Road-Balance/SpotMicroJetson/Images/jetsonNano.jpg

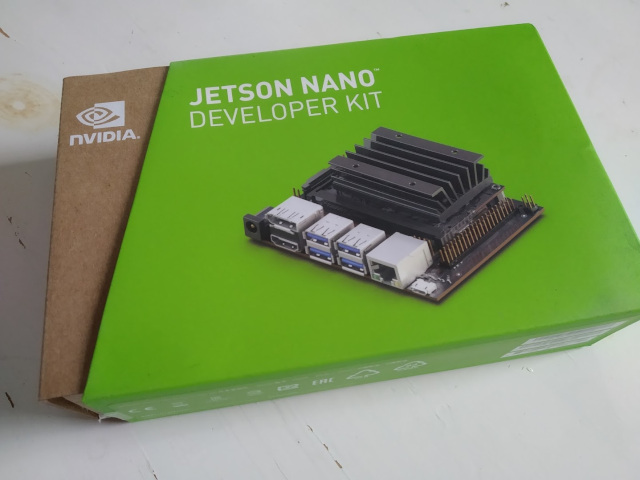
Images/jetsonNano.jpg
