Road-Balance/SpotMicroJetson/Images/jetsonNano_connected_1.jpg

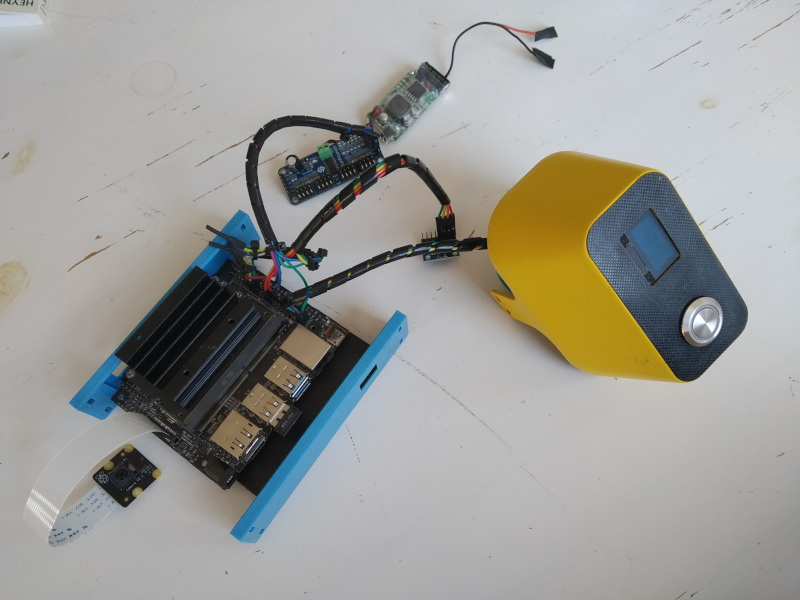
Images/jetsonNano_connected_1.jpg
