Road-Balance/SpotMicroJetson/Images/jetsonNanoCase.jpg

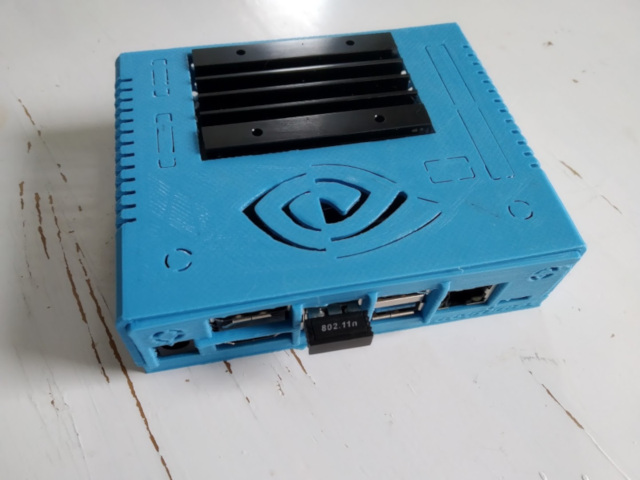
Images/jetsonNanoCase.jpg
