Road-Balance/SpotMicroJetson/Images/leg_front.jpg

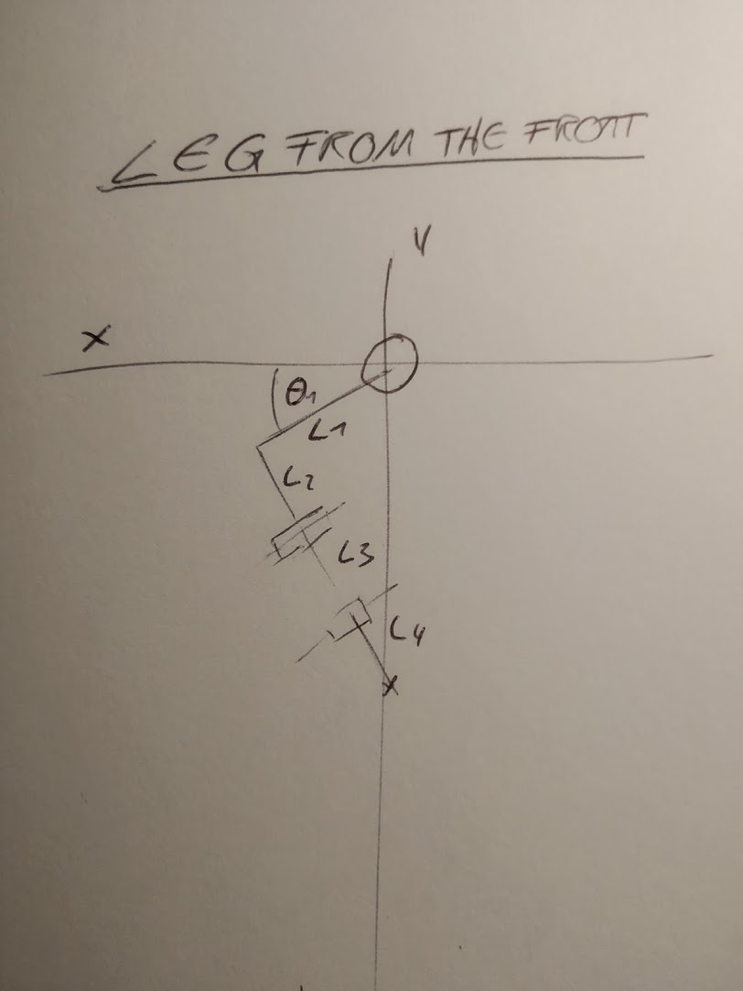
Images/leg_front.jpg
