Road-Balance/SpotMicroJetson/Images/leg_front_solved.jpg

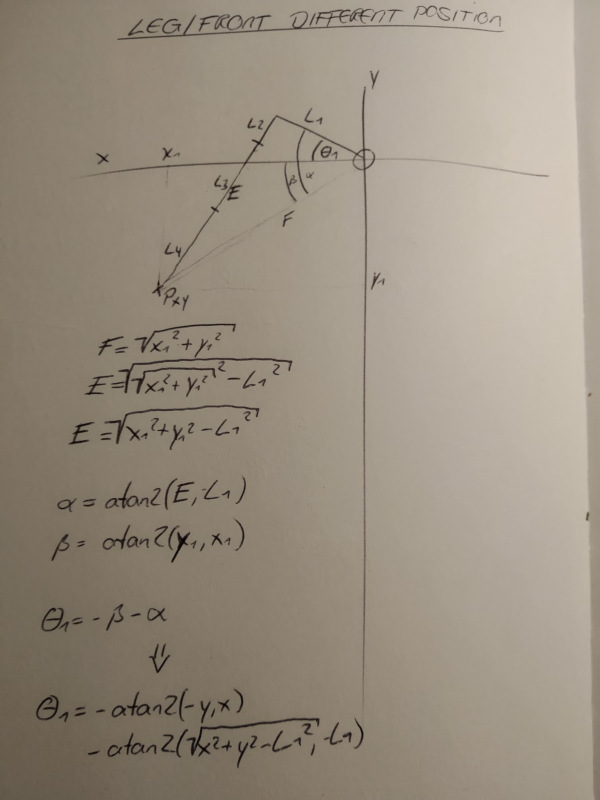
Images/leg_front_solved.jpg
