Road-Balance/SpotMicroJetson/Images/leg_in_space.jpg

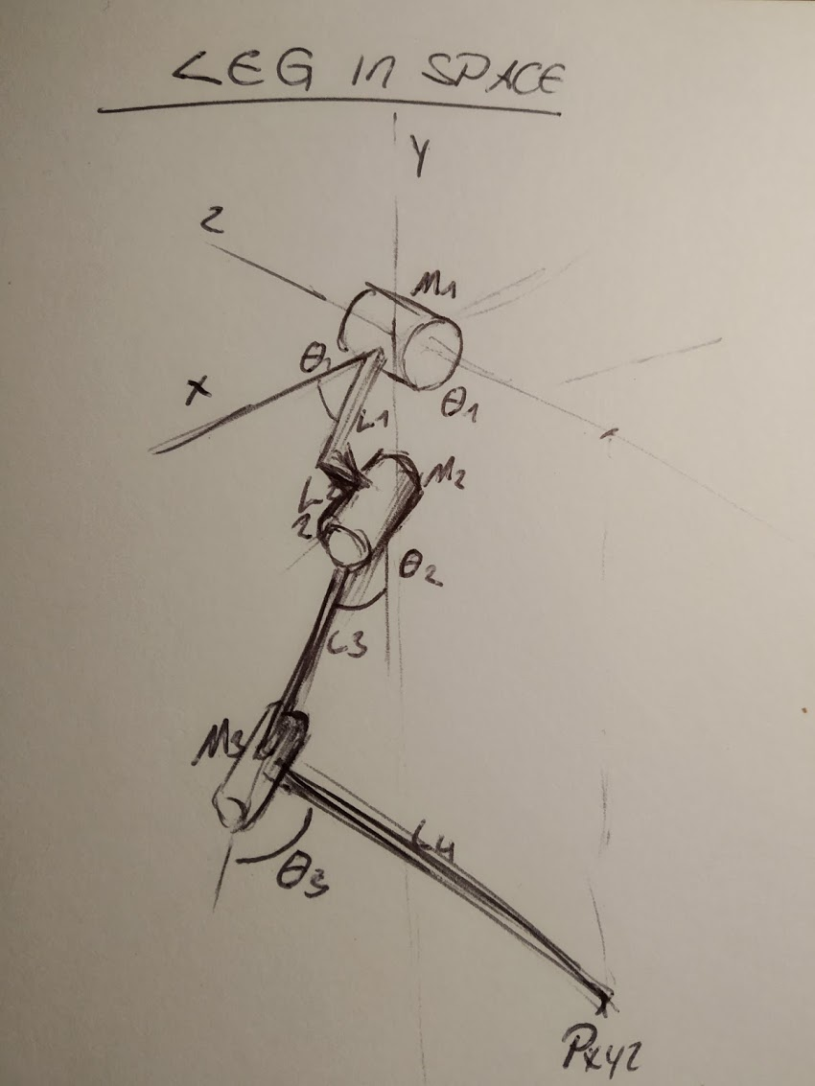
Images/leg_in_space.jpg
