Road-Balance/SpotMicroJetson/Images/leg_side.jpg

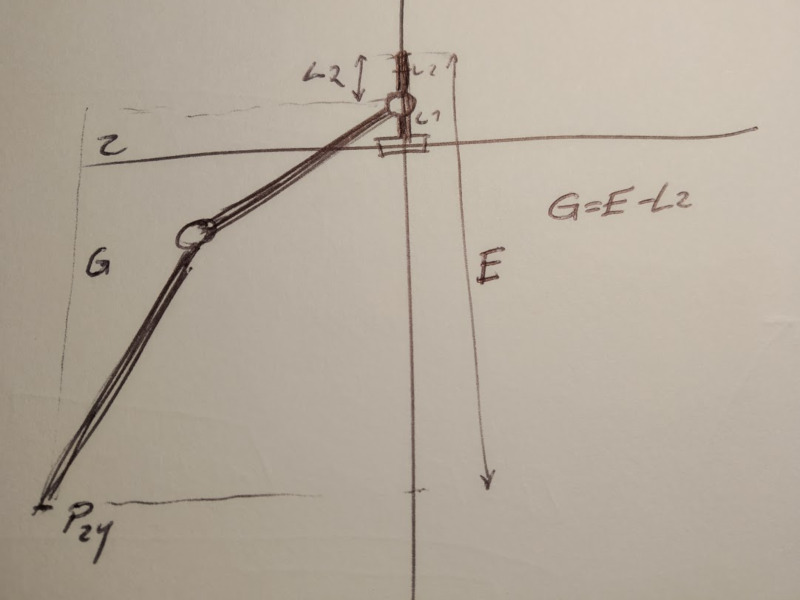
Images/leg_side.jpg
