Road-Balance/SpotMicroJetson/Images/leg_side_2.jpg

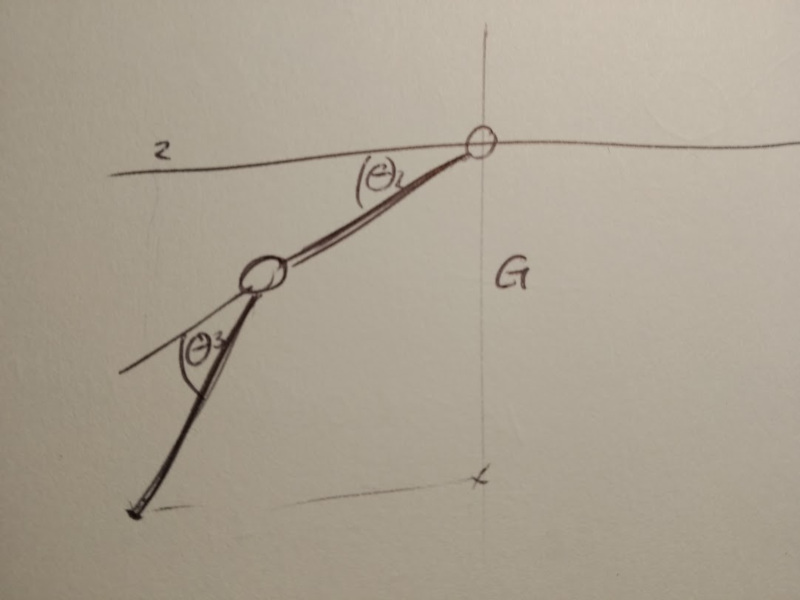
Images/leg_side_2.jpg
