Road-Balance/SpotMicroJetson/Images/leg_side_g.jpg

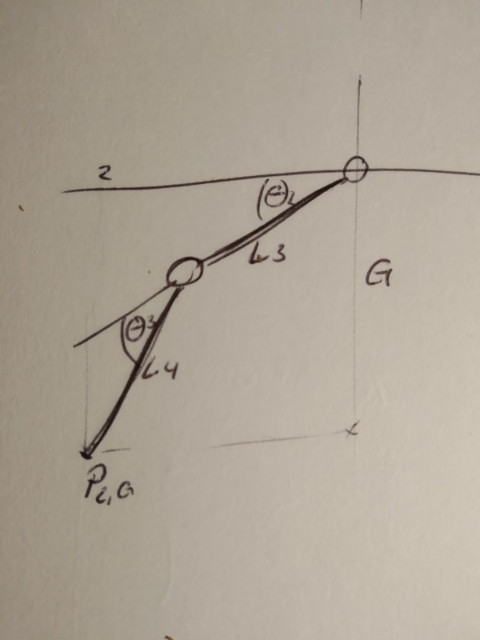
Images/leg_side_g.jpg
