Road-Balance/SpotMicroJetson/Images/SpotMicroAI_1.jpg

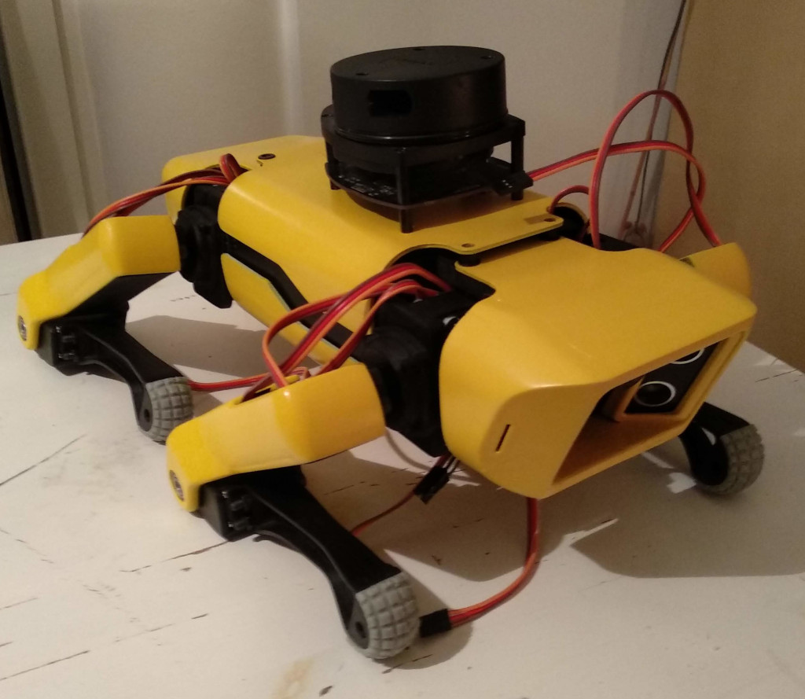
Images/SpotMicroAI_1.jpg
