Road-Balance/SpotMicroJetson/Images/SpotMicroAI_FreeCad.png

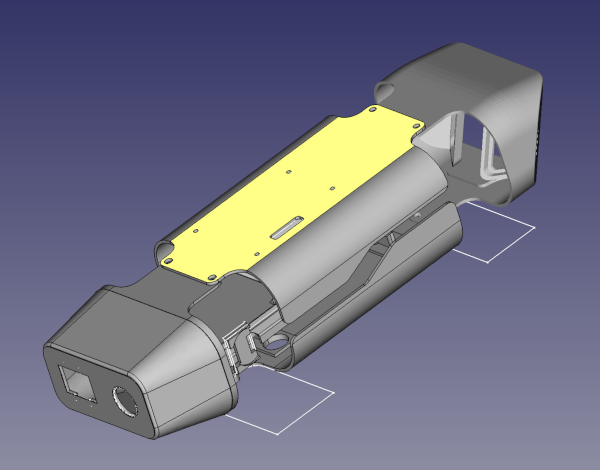
Images/SpotMicroAI_FreeCad.png
