Road-Balance/SpotMicroJetson/Images/SpotMicroAI_pybullet.png

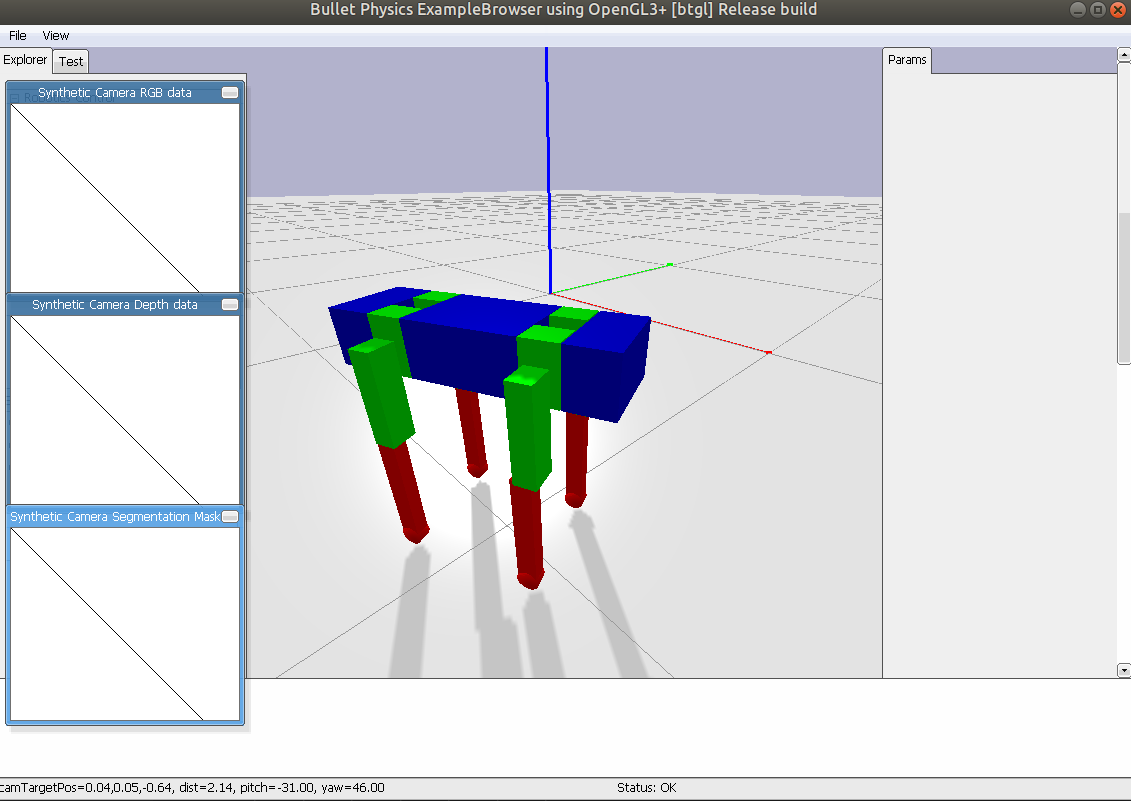
Images/SpotMicroAI_pybullet.png
