Road-Balance/SpotMicroJetson/Images/SpotMicroAI_pybullet_2.png

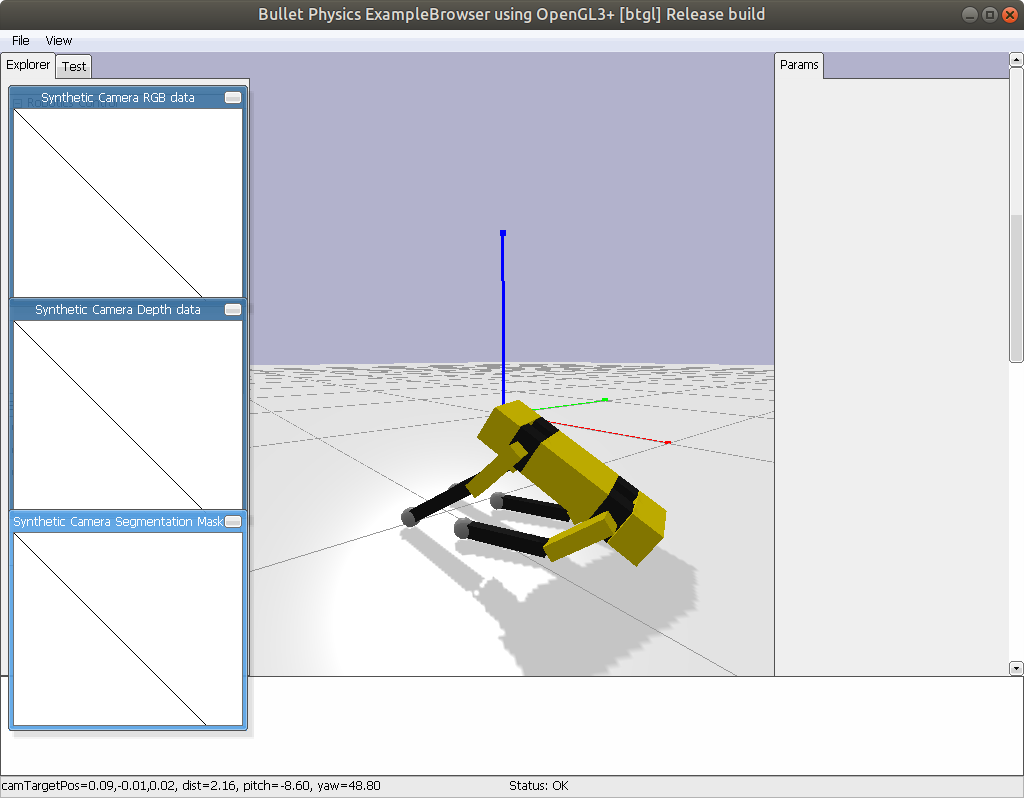
Images/SpotMicroAI_pybullet_2.png
