Road-Balance/SpotMicroJetson/Images/SpotMicroAI_pybullet_lidar2.png

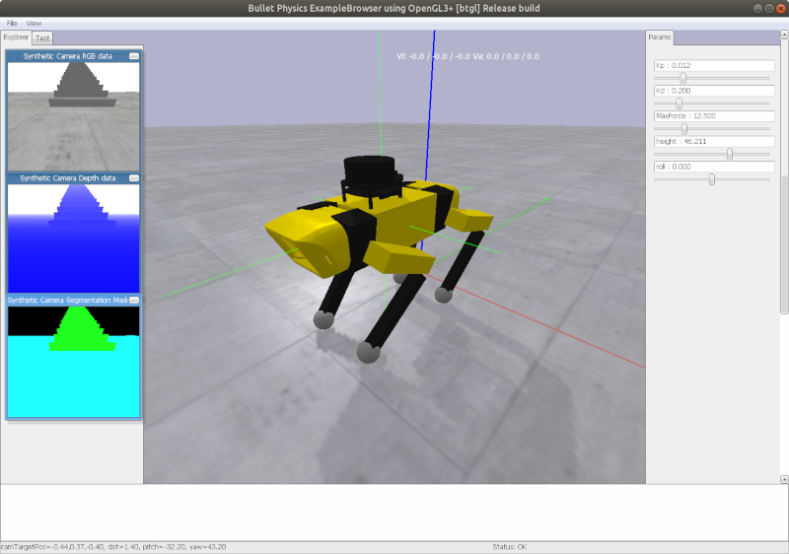
Images/SpotMicroAI_pybullet_lidar2.png
