Road-Balance/SpotMicroJetson/Images/SpotMicroAI_pybullet_lidar3.png

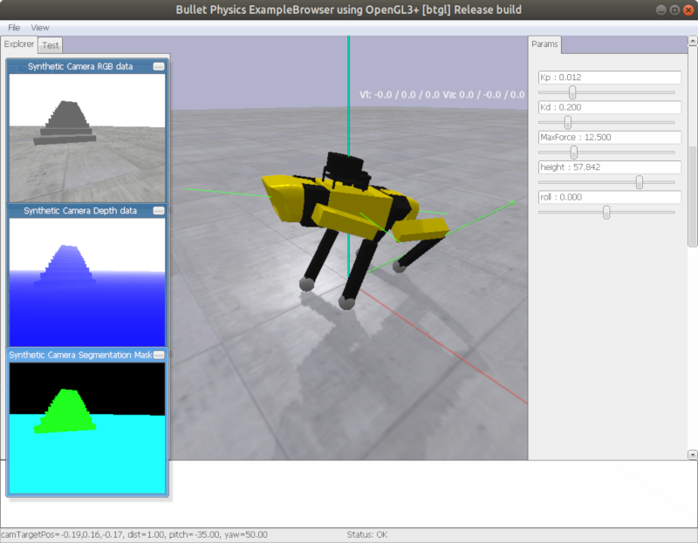
Images/SpotMicroAI_pybullet_lidar3.png
