Road-Balance/SpotMicroJetson/Images/SpotMicroAI_rviz_2.png

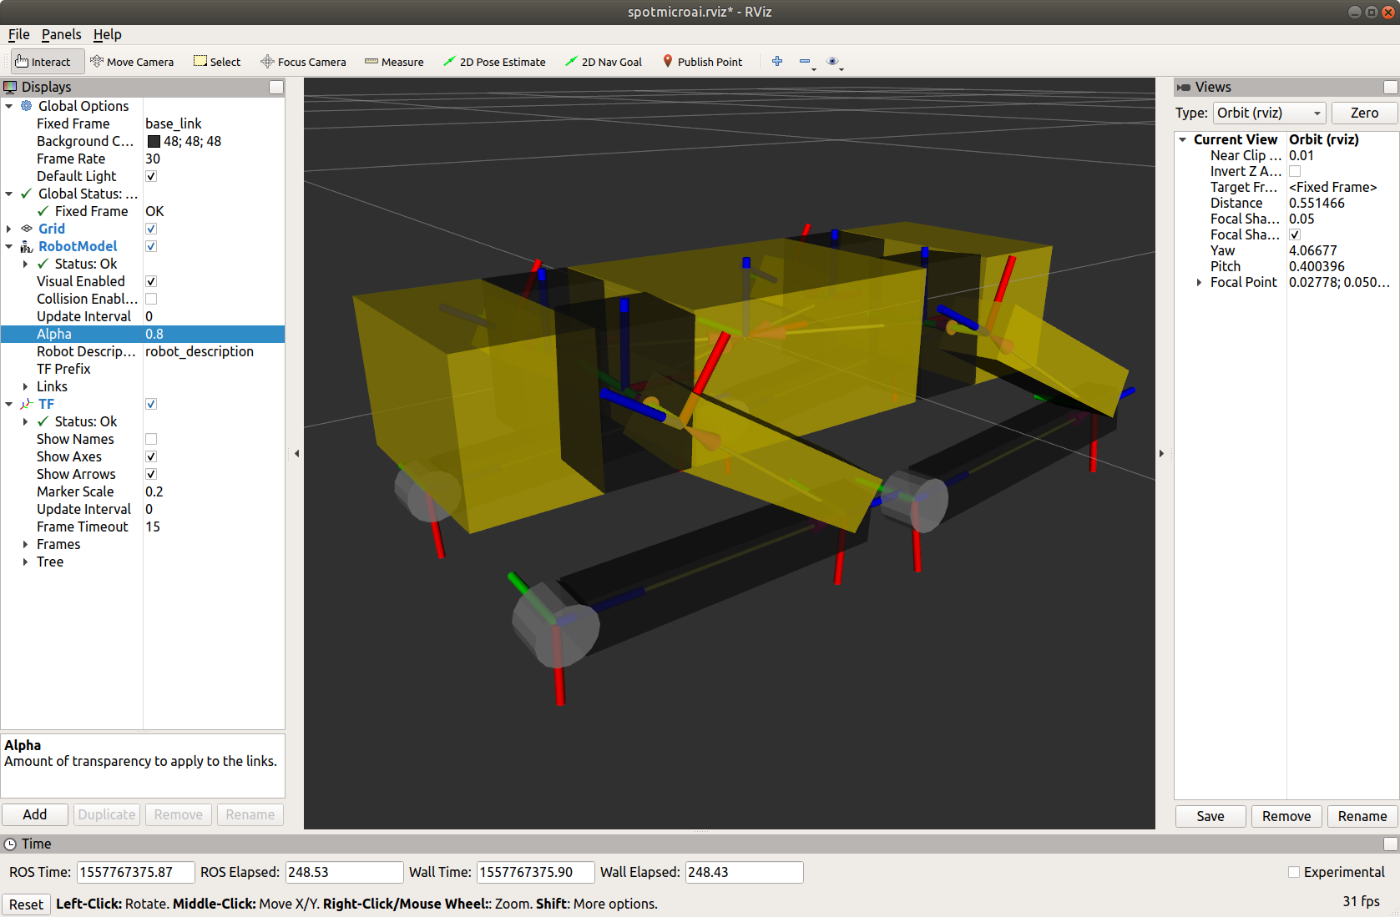
Images/SpotMicroAI_rviz_2.png
