Road-Balance/SpotMicroJetson/Images/SpotMicroAI_rviz_urdf.png

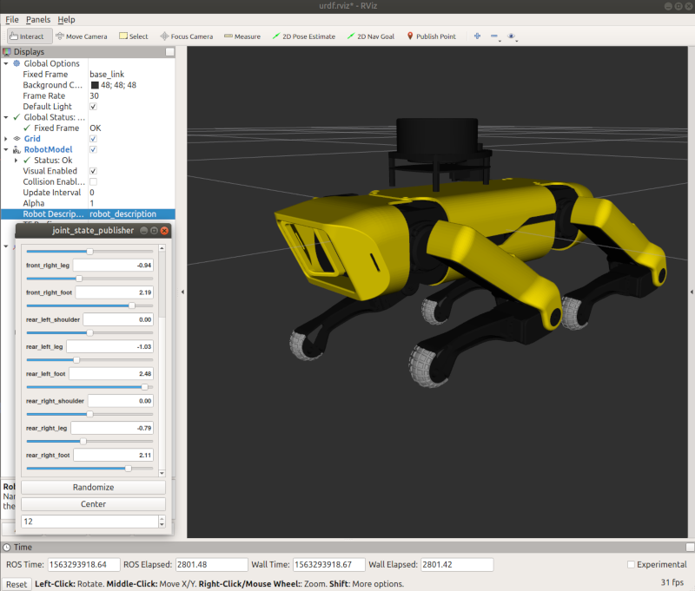
Images/SpotMicroAI_rviz_urdf.png
