Road-Balance/SpotMicroJetson/Images/SpotMicroAI_urdf2.png

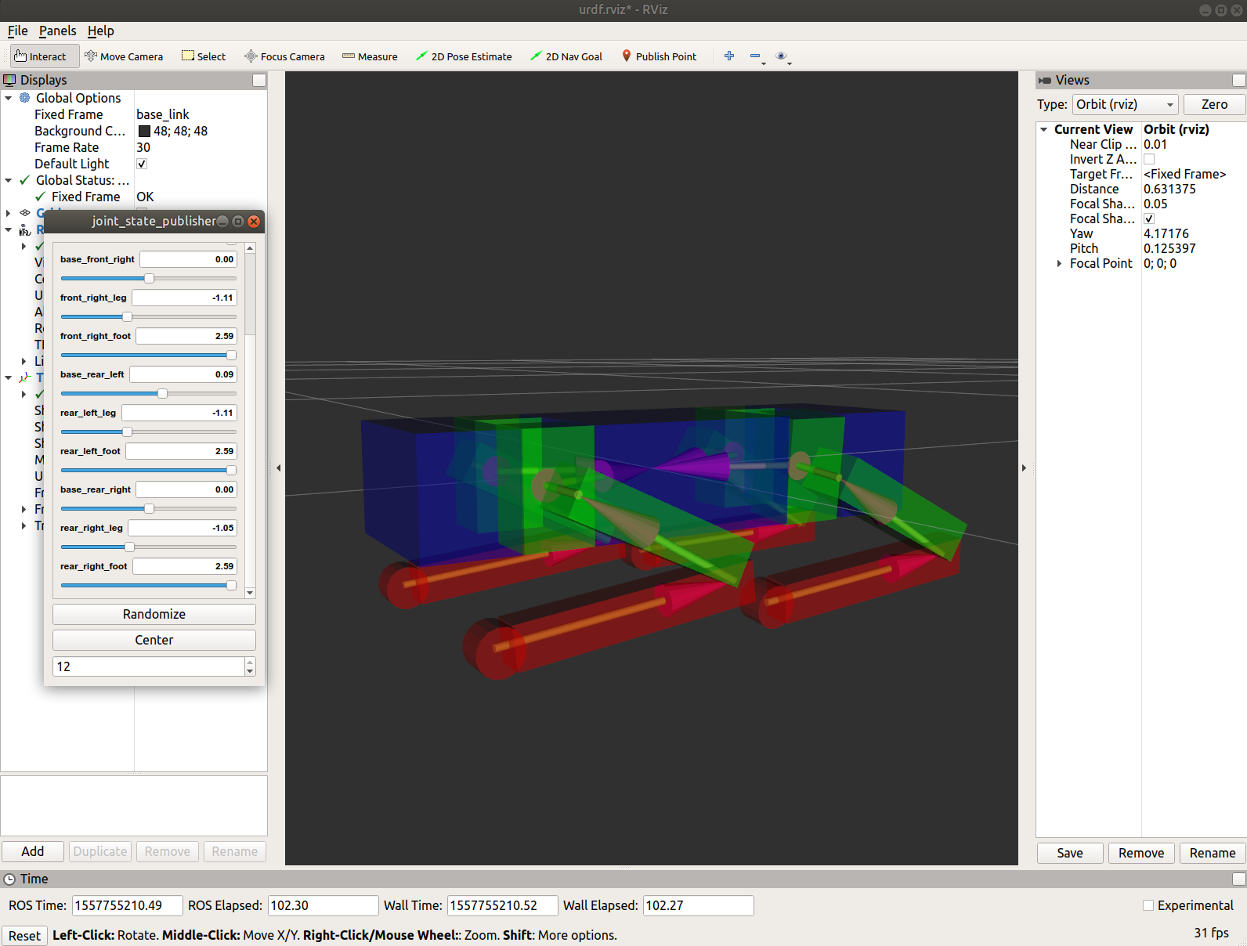
Images/SpotMicroAI_urdf2.png
