Road-Balance/SpotMicroJetson/Images/SpotMicroAI_urdf.png

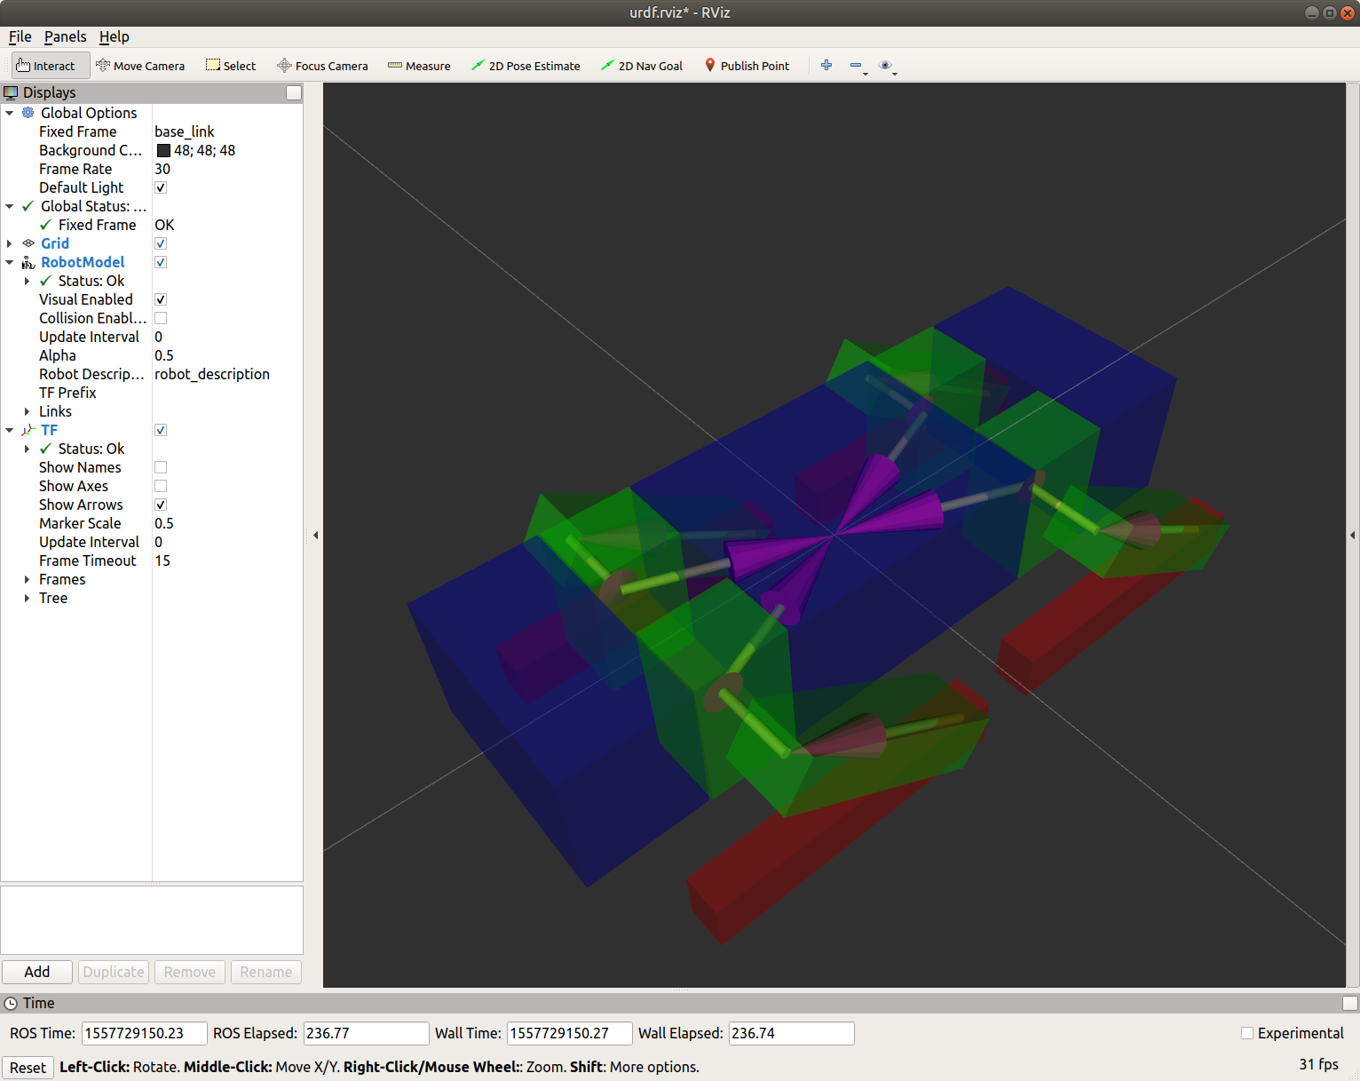
Images/SpotMicroAI_urdf.png
