Road-Balance/SpotMicroJetson/Simulation/asphalt.png

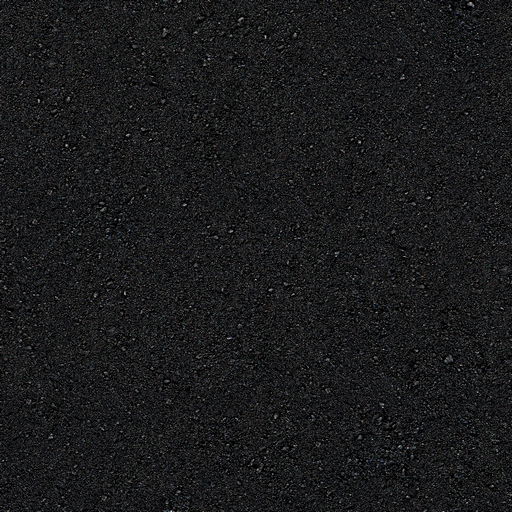
Simulation/asphalt.png
