Road-Balance/SpotMicroJetson/Simulation/concrete2.png

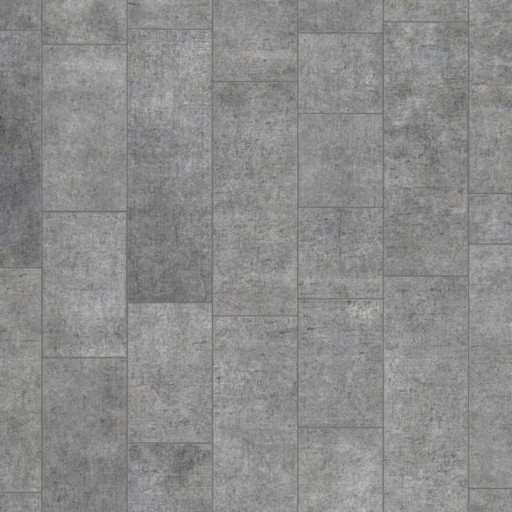
Simulation/concrete2.png
