Road-Balance/SpotMicroJetson/Simulation/concrete.png

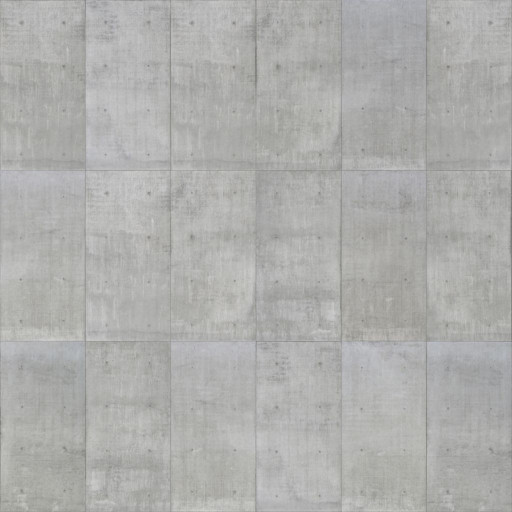
Simulation/concrete.png
