Road-Balance/SpotMicroJetson/Simulation/image/wasd_keyboard_buttons.jpg

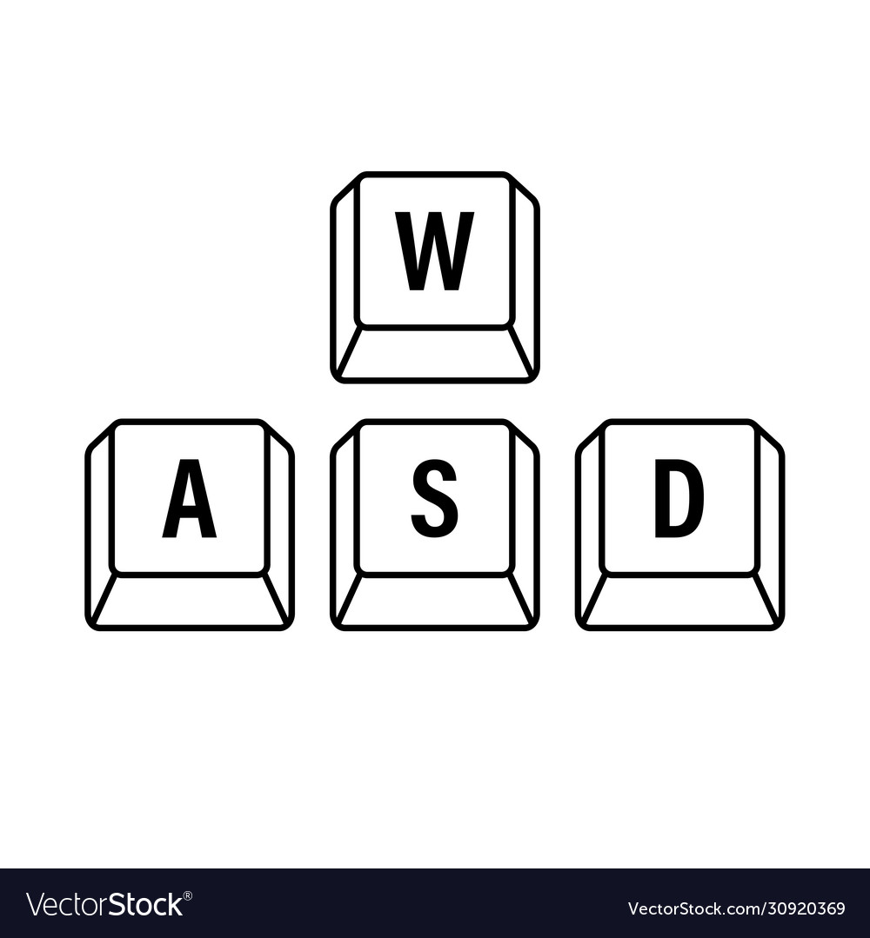
Simulation/image/wasd_keyboard_buttons.jpg
