Road-Balance/SpotMicroJetson/Images/STL_Parts.jpg

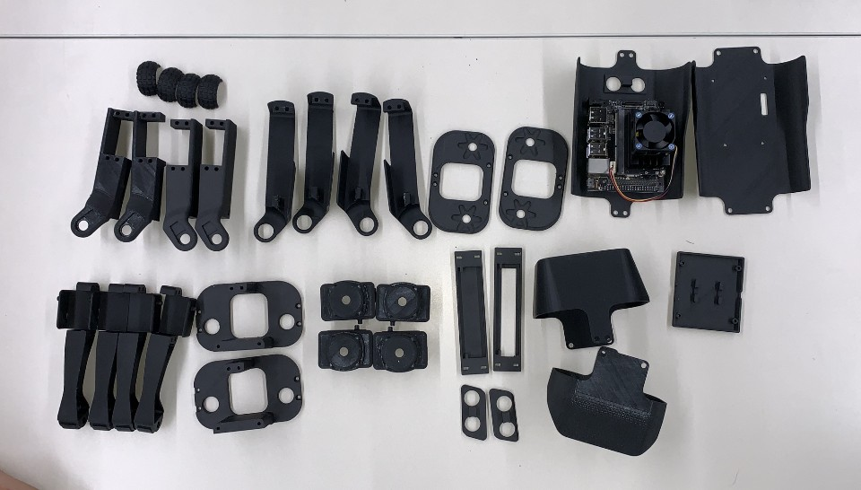
Images/STL_Parts.jpg
