Road-Balance/SpotMicroJetson/STL/bottom.stl

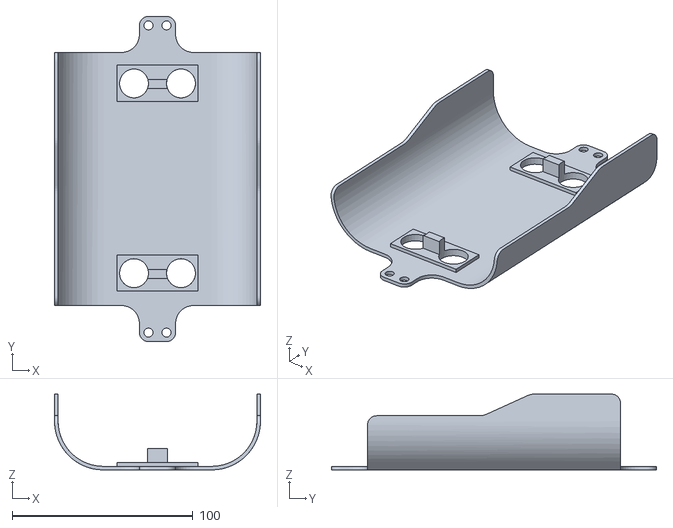
[picture p48: CAD file, 2020-09-26]
STL/bottom.stl
114.0 x 180.0 x 42.0
