Road-Balance/SpotMicroJetson/urdf/FreeCAD/SpotMicroAI_Top.FCStd

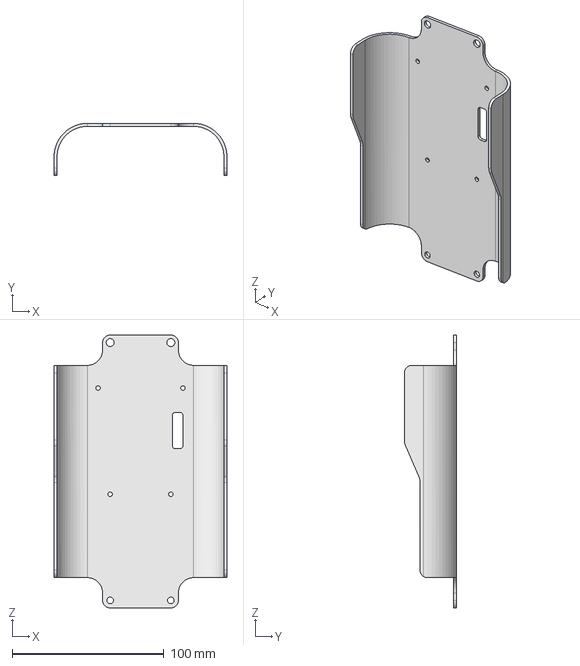
[picture p49: CAD file, 2020-09-26]
urdf/FreeCAD/SpotMicroAI_Top.FCStd
114.0 x 34.5 x 180.0 mm
