Road-Balance/SpotMicroJetson/Parts/lfoot.stl

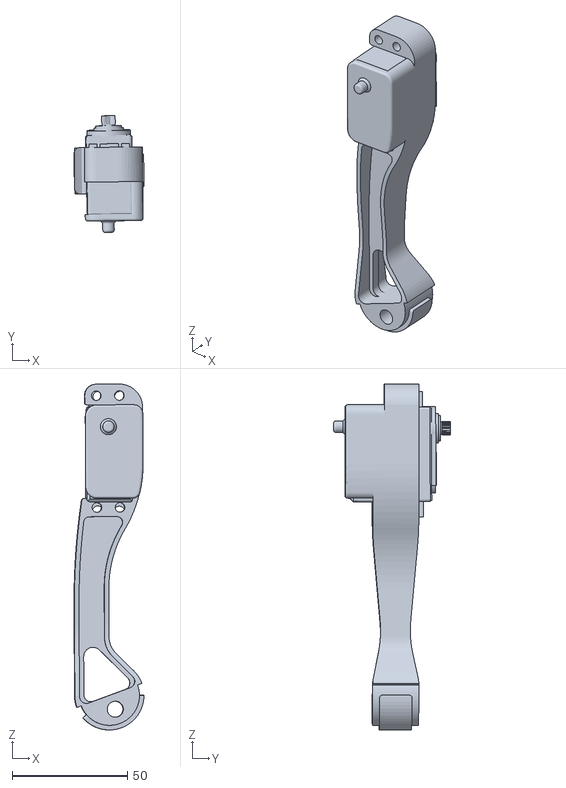
[picture p50: CAD file, 2020-09-26]
Parts/lfoot.stl
30.4 x 50.7 x 150.0
