Road-Balance/SpotMicroJetson/STEP_Files/L_Side_Plate_modi(Long).stp

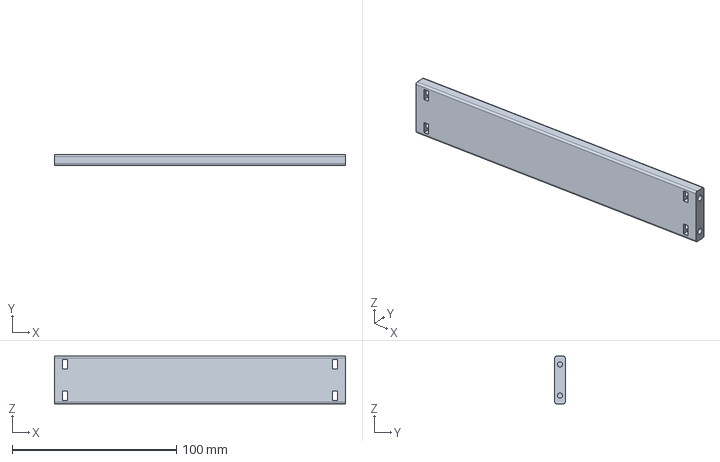
[picture p51: CAD file, 2021-01-22]
STEP_Files/L_Side_Plate_modi(Long).stp
177.0 x 6.50 x 29.0 mm
