Road-Balance/SpotMicroJetson/STL/files/non-mega_T_cover.stl

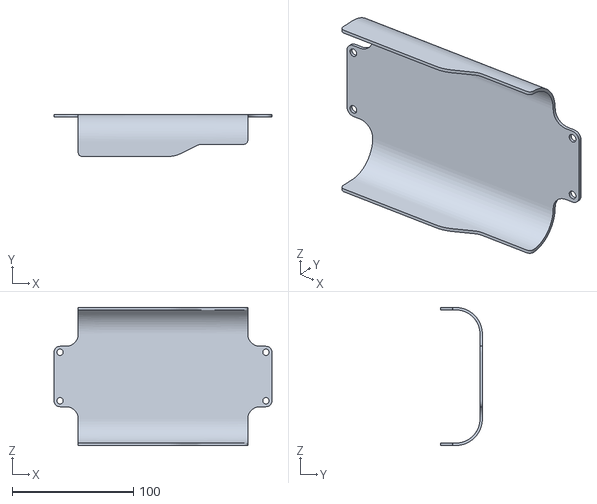
[picture p52: CAD file, 2020-09-26]
STL/files/non-mega_T_cover.stl
180.0 x 34.5 x 114.0
