Road-Balance/SpotMicroJetson/STL/top.stl

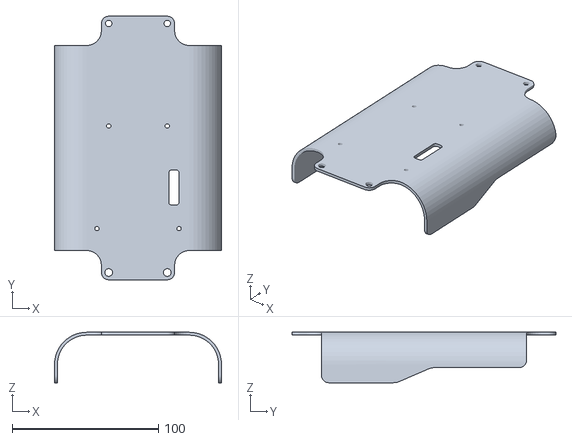
[picture p53: CAD file, 2020-09-26]
STL/top.stl
114.0 x 180.0 x 34.5
