Road-Balance/SpotMicroJetson/STEP_Files/R_Side_Plate_modi(long).stp

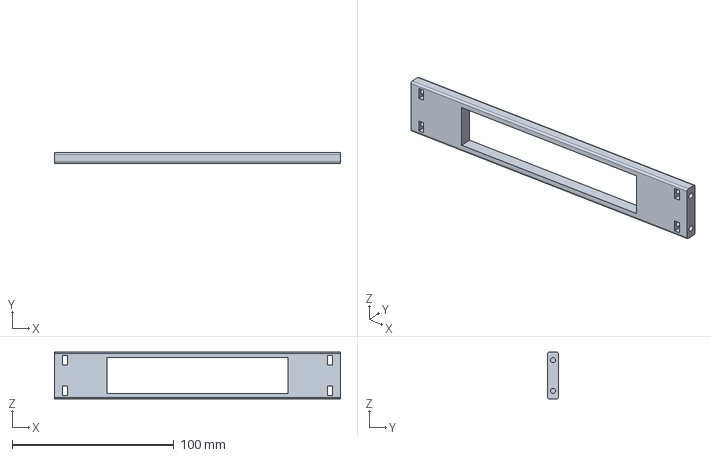
[picture p54: CAD file, 2021-01-22]
STEP_Files/R_Side_Plate_modi(long).stp
177.0 x 6.50 x 29.0 mm
