Road-Balance/SpotMicroJetson/STL/files/R_arm_joint.stl

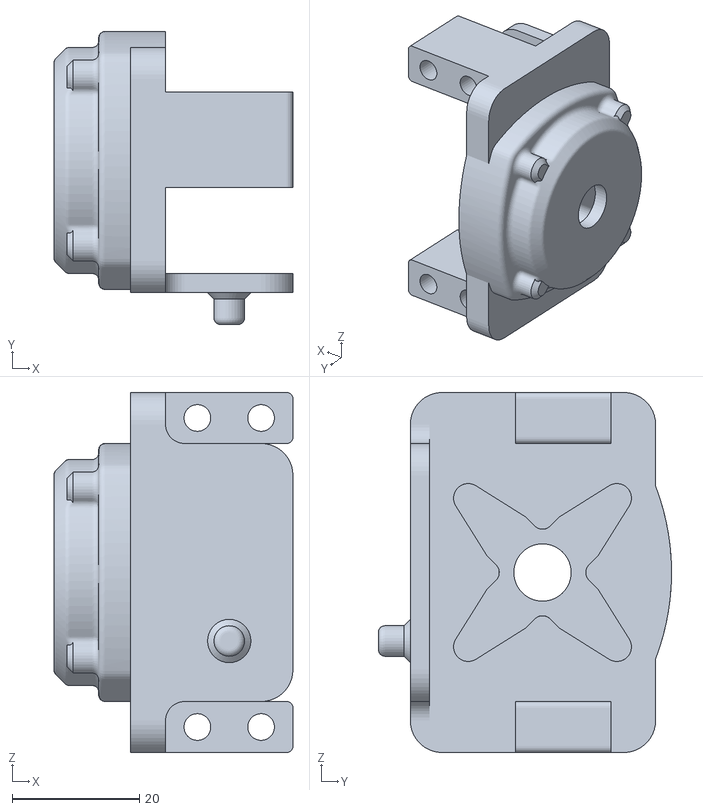
[picture p55: CAD file, 2020-09-26]
STL/files/R_arm_joint.stl
37.5 x 46.0 x 56.5
