Road-Balance/SpotMicroJetson/STL/testmount.stl

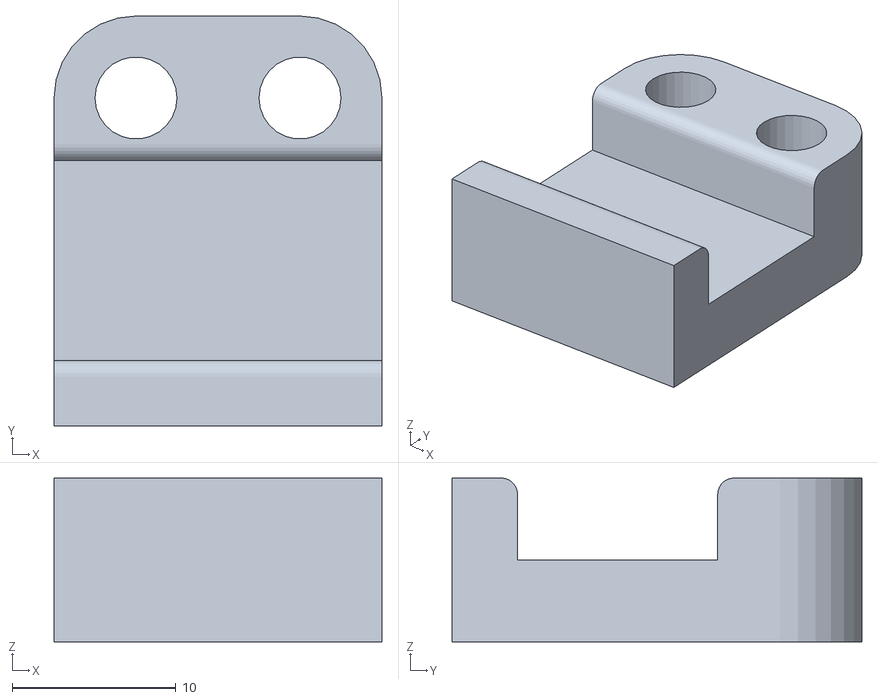
[picture p56: CAD file, 2020-09-26]
STL/testmount.stl
20.0 x 25.0 x 10.0
