Road-Balance/SpotMicroJetson/Parts/rarm.stl

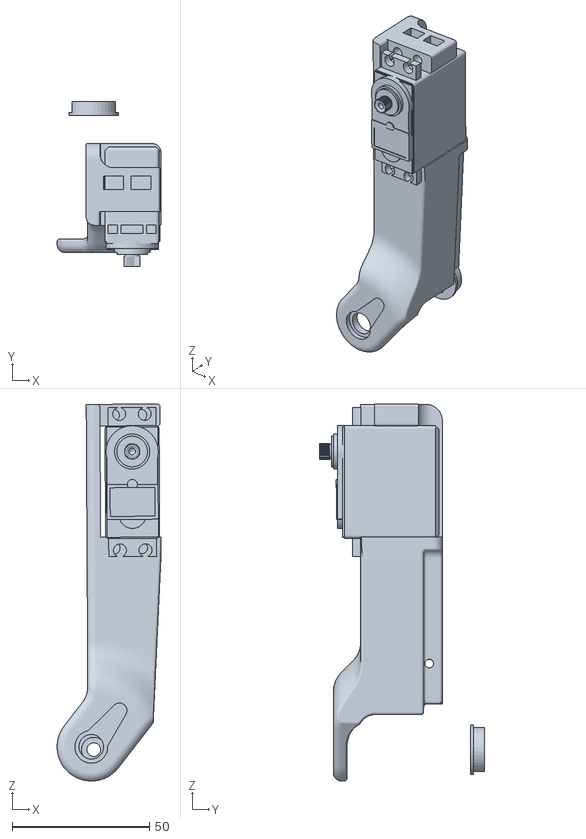
[picture p57: CAD file, 2020-09-26]
Parts/rarm.stl
37.9 x 60.2 x 137.5
