Road-Balance/SpotMicroJetson/STL/files/F_cover_orig.stl

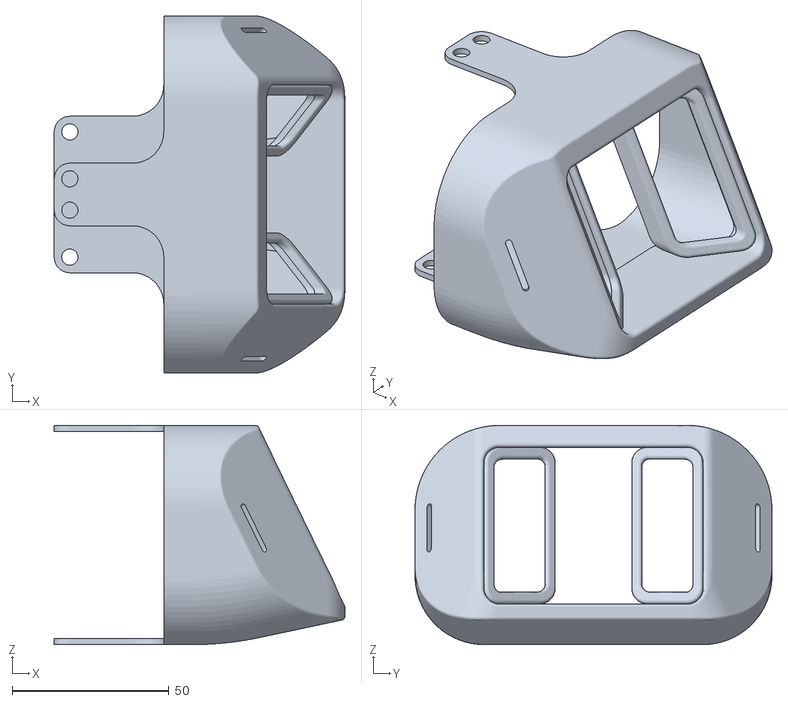
[picture p58: CAD file, 2020-09-26]
STL/files/F_cover_orig.stl
92.8 x 114.0 x 70.0
