Road-Balance/SpotMicroJetson/STL/ledholder.stl

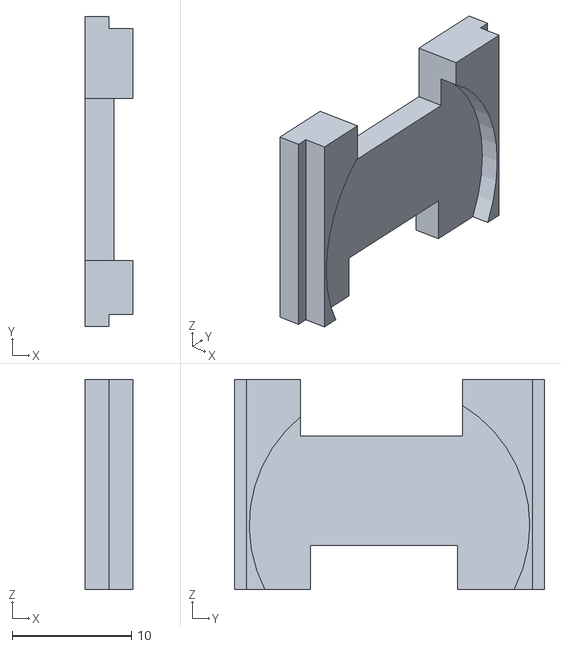
[picture p59: CAD file, 2020-09-26]
STL/ledholder.stl
4.00 x 26.0 x 17.6
