Road-Balance/SpotMicroJetson/Parts/rarm_cover.stl

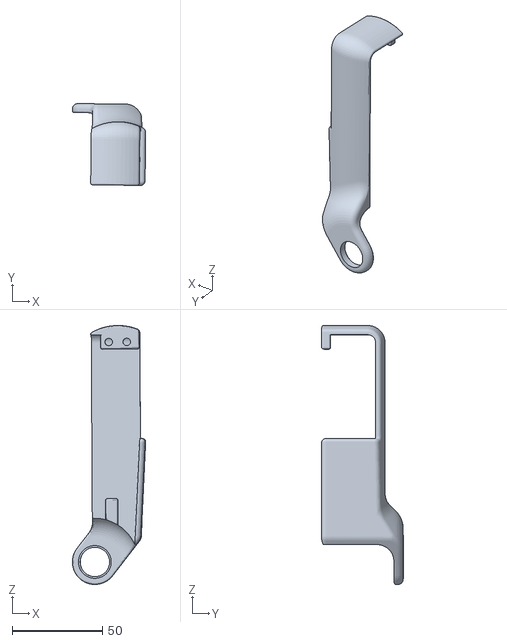
[picture p60: CAD file, 2020-09-26]
Parts/rarm_cover.stl
40.7 x 45.4 x 143.6
