Road-Balance/SpotMicroJetson/STL/files/B_cover.stl

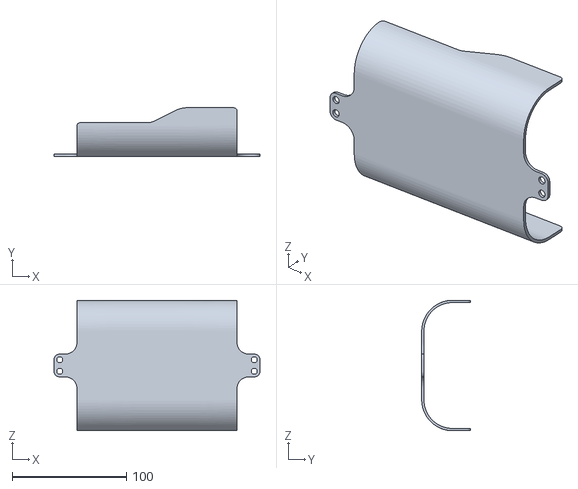
[picture p61: CAD file, 2020-09-26]
STL/files/B_cover.stl
180.0 x 42.5 x 114.0
