Road-Balance/SpotMicroJetson/Parts/jetson_sidepart.stl

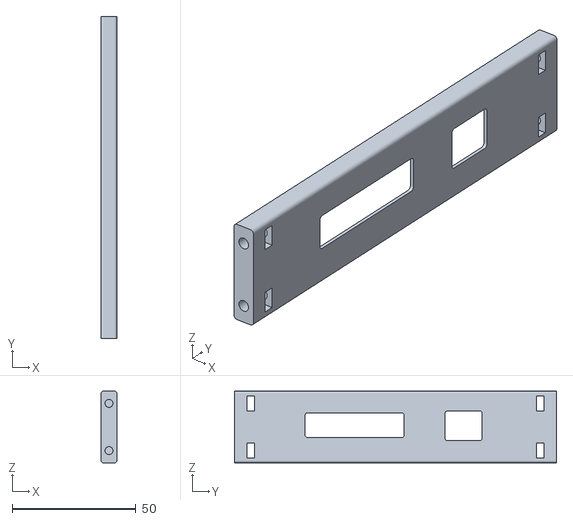
[picture p62: CAD file, 2020-09-26]
Parts/jetson_sidepart.stl
6.50 x 130.0 x 29.0
