Road-Balance/SpotMicroJetson/STL/batteryholder.stl

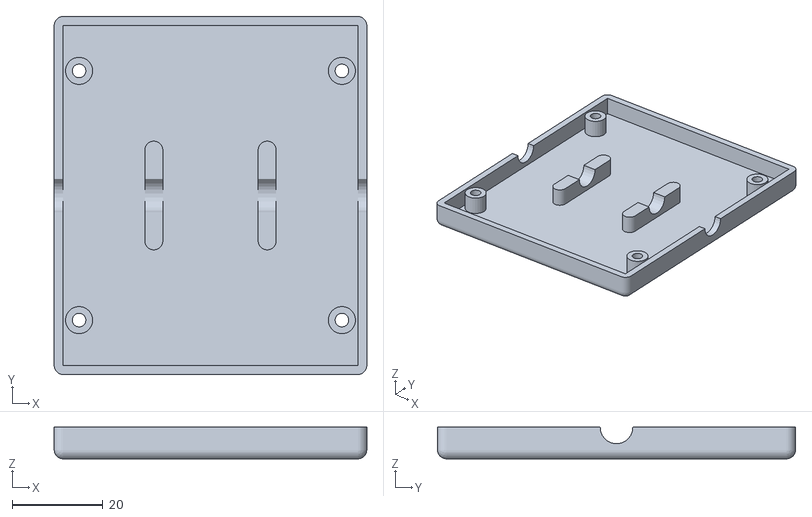
[picture p63: CAD file, 2020-09-26]
STL/batteryholder.stl
69.0 x 79.0 x 7.00
