Road-Balance/SpotMicroJetson/STL/files/L_wrist.stl

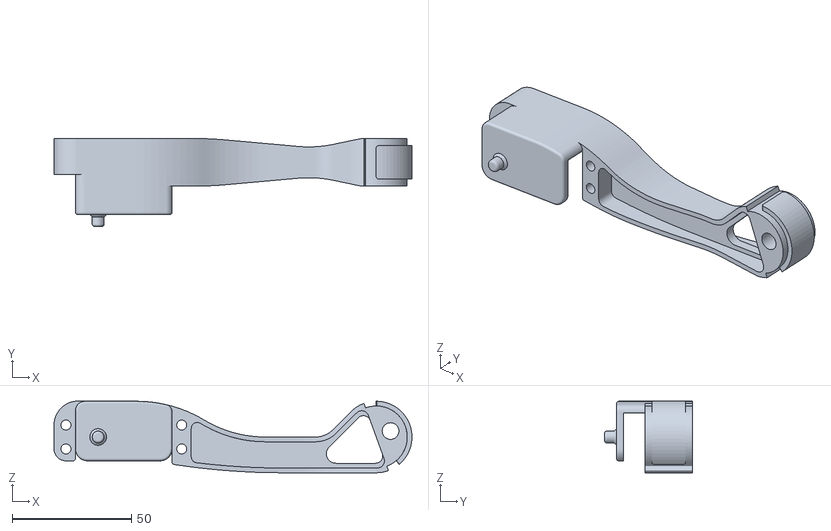
[picture p64: CAD file, 2020-09-26]
STL/files/L_wrist.stl
150.0 x 36.9 x 30.0
