Road-Balance/SpotMicroJetson/Parts/frontpart.stl

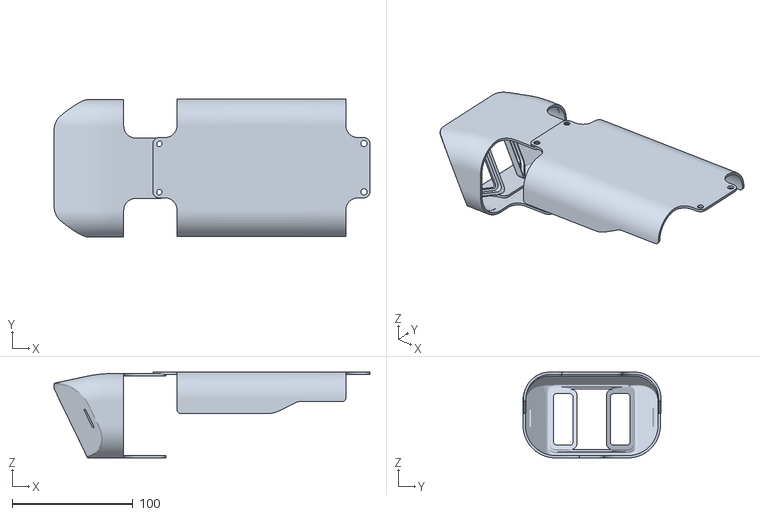
[picture p65: CAD file, 2020-09-26]
Parts/frontpart.stl
262.0 x 114.5 x 71.2
