Road-Balance/SpotMicroJetson/STL/files/R_cover.stl

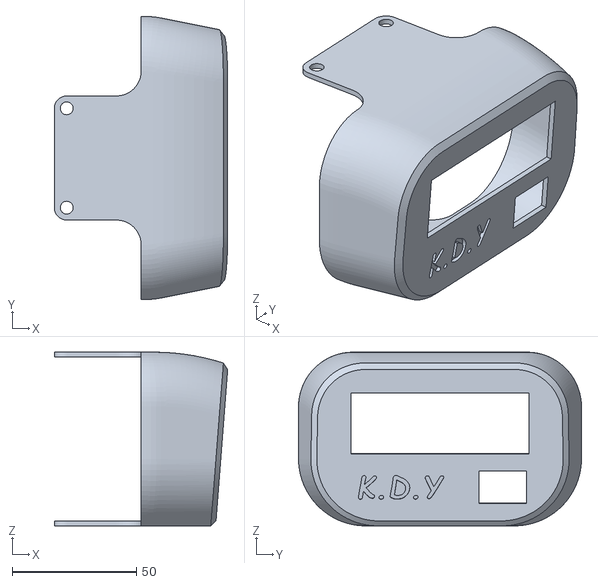
[picture p66: CAD file, 2020-09-26]
STL/files/R_cover.stl
69.8 x 114.0 x 70.0
