Road-Balance/SpotMicroJetson/STL/label.stl

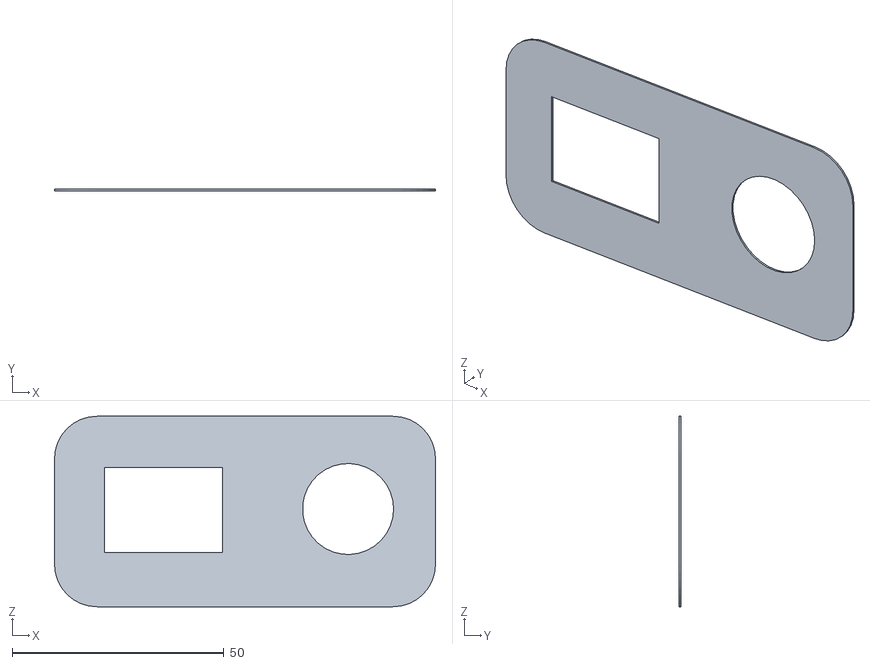
[picture p67: CAD file, 2020-09-26]
STL/label.stl
90.0 x 0.4 x 45.0
