Road-Balance/SpotMicroJetson/STL/files/foot.stl

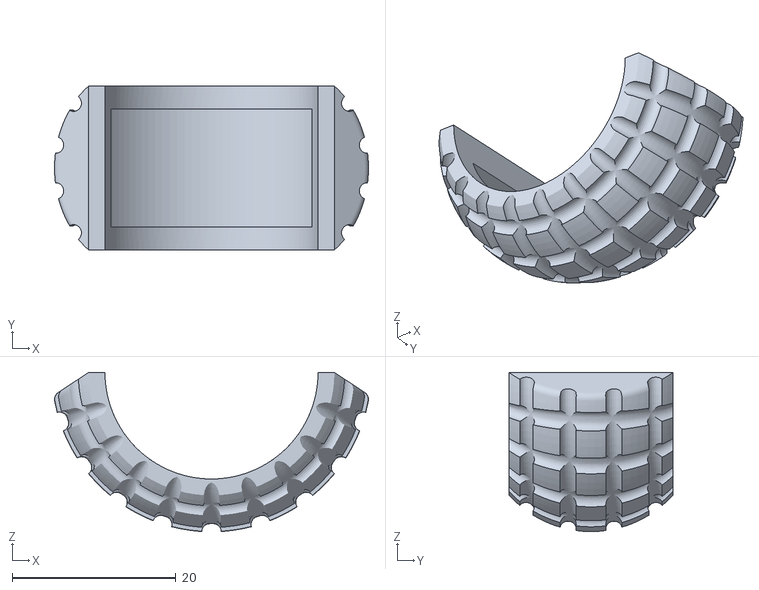
[picture p68: CAD file, 2020-09-26]
STL/files/foot.stl
38.3 x 20.0 x 19.4
