Road-Balance/SpotMicroJetson/STL/files/plate.stl

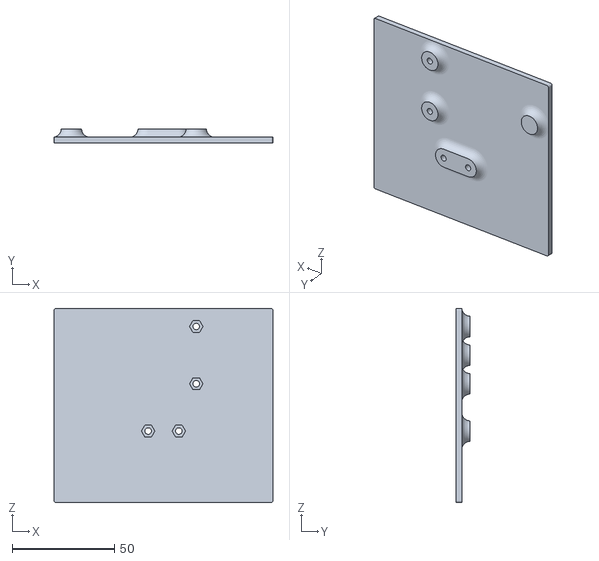
[picture p69: CAD file, 2020-09-26]
STL/files/plate.stl
107.0 x 7.00 x 95.0
