Road-Balance/SpotMicroJetson/Parts/backpart.stl

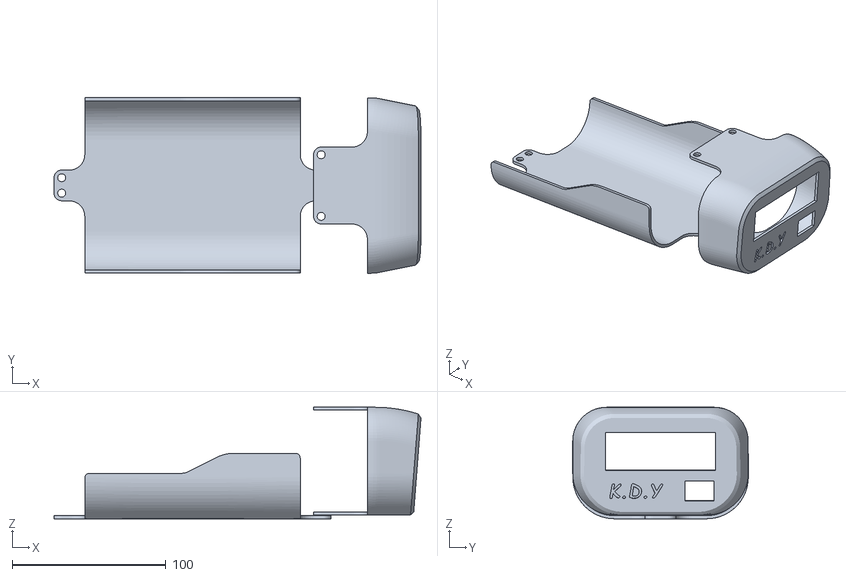
[picture p70: CAD file, 2020-09-26]
Parts/backpart.stl
238.4 x 114.1 x 72.5
