Road-Balance/SpotMicroJetson/Parts/jetsonPlate.stl

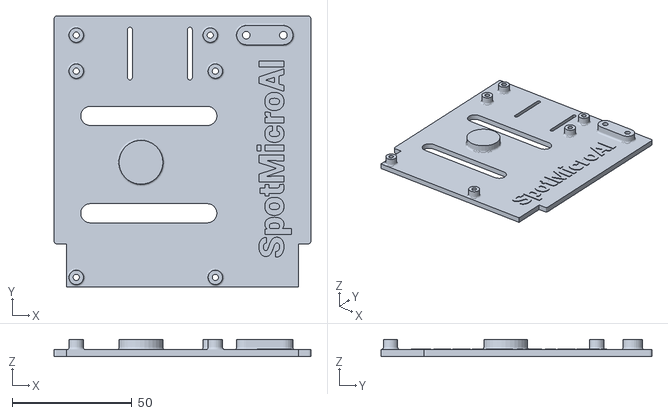
[picture p71: CAD file, 2020-09-26]
Parts/jetsonPlate.stl
107.0 x 113.0 x 7.10
