Road-Balance/SpotMicroJetson/Images/Readme_assemble.jpg

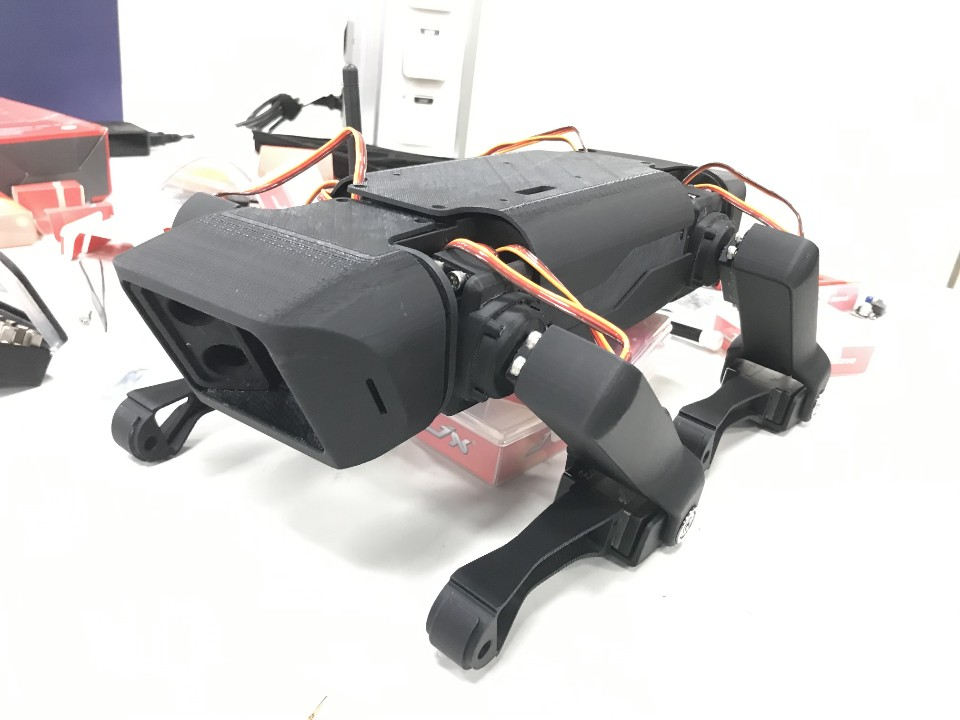
Images/Readme_assemble.jpg
