Road-Balance/SpotMicroJetson/JetsonNano/start_robot.py

import time
import math
import numpy as np
from kinematics import Kinematic
from servos import Servos

class RobotRunner:

    def __init__(self):
        print("Initialising")
        self.servos=Servos()
        self.Kinematic=Kinematic()

    def calibrate(self):
        print("Running")
        while True:
            servo=int(input("Enter Servo to calibrate (0-12)"))
            # print("Current Offset is {}".format(self.servos.getServoOffset(servo)))
            offset=int(input("Enter new Offset:"))
            self.servos.angle(servo,offset)


RobotRunner().calibrate()
