Road-Balance/SpotMicroJetson/JetsonNano/motor_test.py

from adafruit_pca9685 import PCA9685
from adafruit_motor import servo

import board
import busio
import time

i2c_bus0=(busio.I2C(board.SCL_1, board.SDA_1))

pca_1 = PCA9685(i2c_bus0, address=0x40)
pca_1.frequency = 60
servo2 = servo.Servo(pca_1.channels[1], min_pulse=460, max_pulse=2450)



sweep = range(1, int(180), +1)
sweep_backward = range(int(180), 1, -1)
while True:
    for degree in sweep :
        print(degree)
        servo2.angle = int(degree)
        time.sleep(0.01)
    for degree in sweep_backward:
        print(degree)
        servo2.angle = int(degree)
        print( servo2.angle )
        time.sleep(0.01)
